CatalinSerafimescu/ZK-4KXPowerSupplyWithFan/KiCAD/board_3d.png

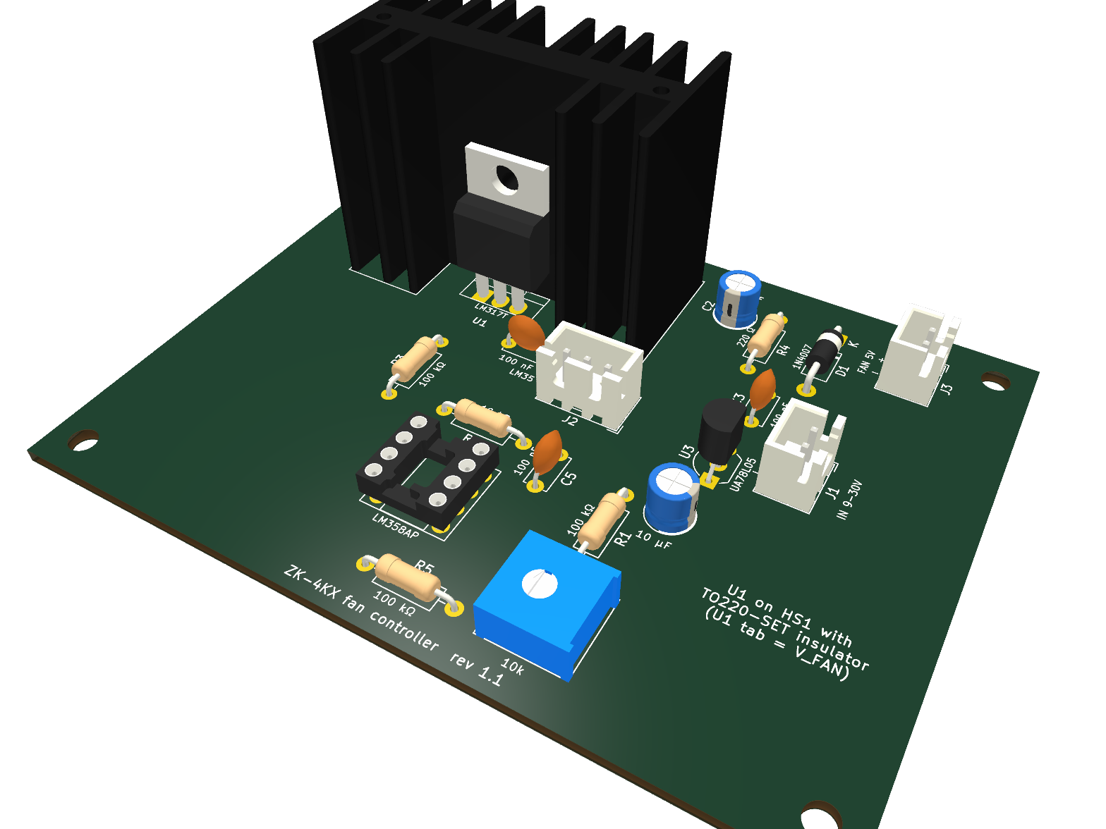
KiCAD/board_3d.png
