CatalinSerafimescu/ZK-4KXPowerSupplyWithFan/KiCAD/board_bottom.png

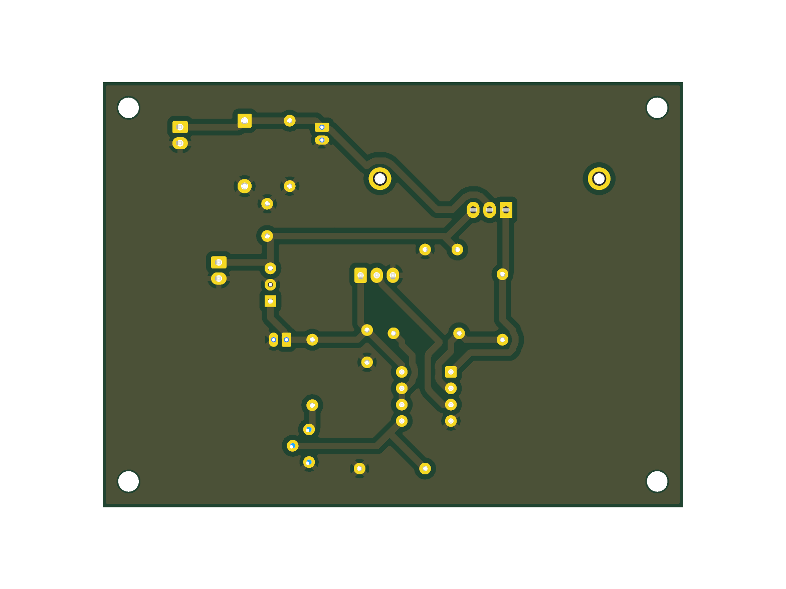
KiCAD/board_bottom.png
