CatalinSerafimescu/ZK-4KXPowerSupplyWithFan/KiCAD/board_top.png

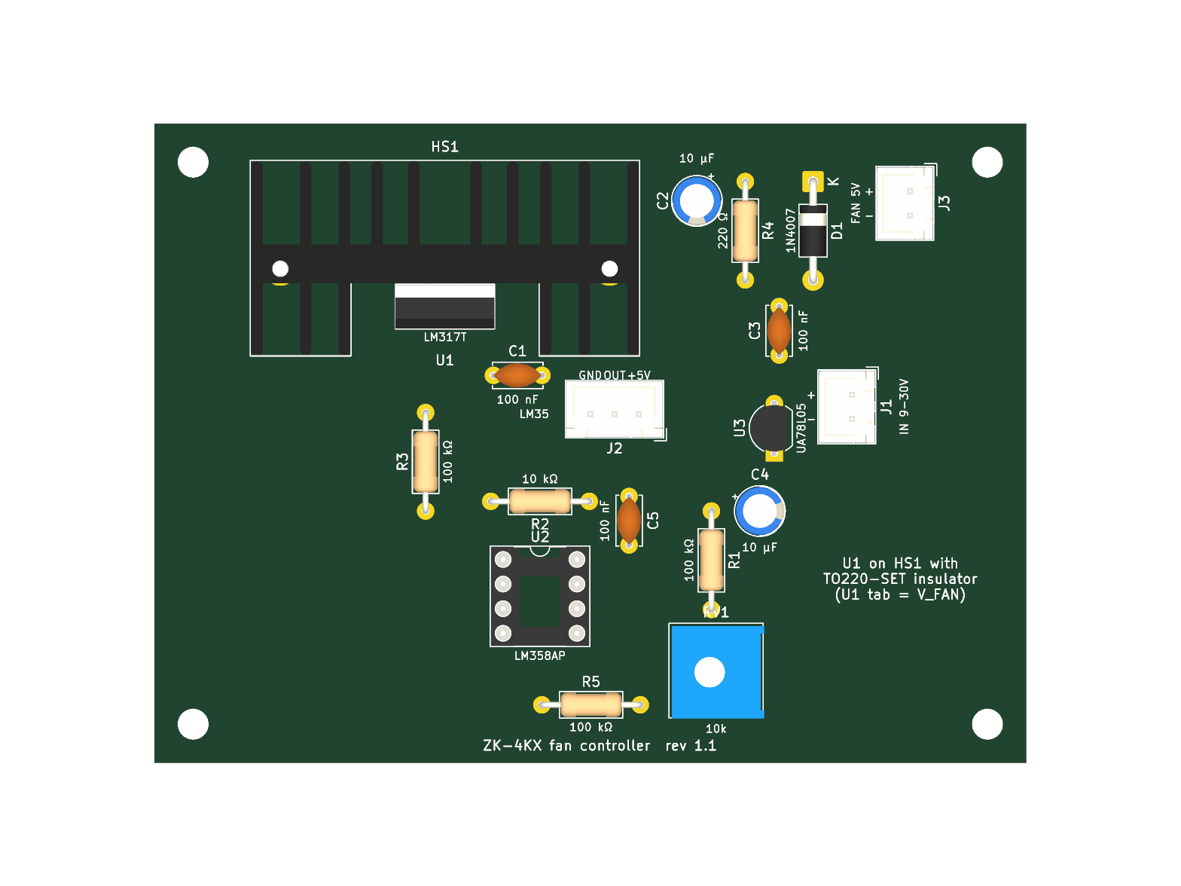
KiCAD/board_top.png
