CatalinSerafimescu/ZK-4KXPowerSupplyWithFan/mechanical/heatsink/RAD-DY-KY.jpg

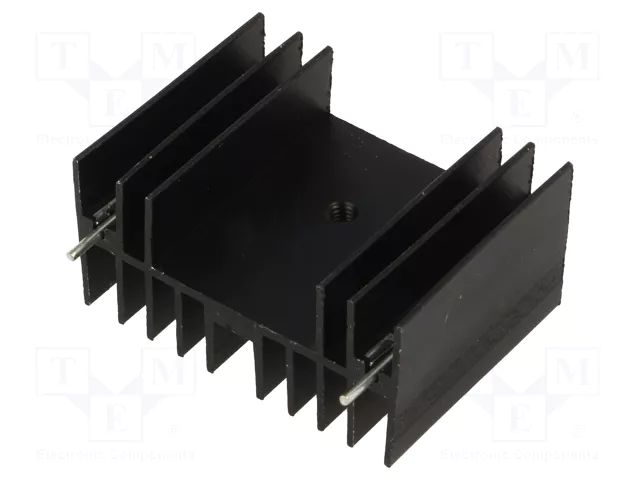
mechanical/heatsink/RAD-DY-KY.jpg
