CatalinSerafimescu/ZK-4KXPowerSupplyWithFan/mechanical/heatsink/RAD-DY-KY_top.jpg

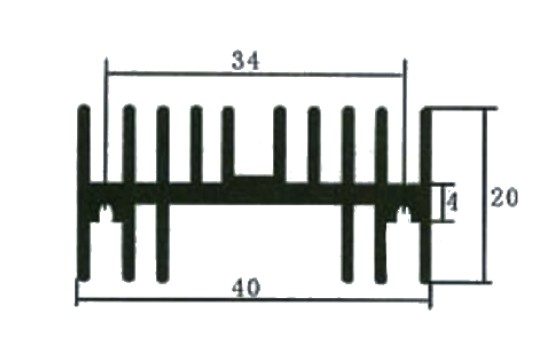
mechanical/heatsink/RAD-DY-KY_top.jpg
