CatalinSerafimescu/ZK-4KXPowerSupplyWithFan/simulation/ltspice/results/A_nominal_40C/out.csv

sweep | vin | t | v5 | vref | vadj | vfan | i317 | ifan
0.0 | 9.0 | 0.0 | 4.999919419615976 | 0.2852405573990915 | 0.006050843584329956 | 1.2532594928394667 | 0.05582701489726584 | 0.05013037971357867
0.25 | 9.0 | 0.25 | 4.999919419615976 | 0.2852405573990915 | 0.006050843584329956 | 1.2532594928394667 | 0.05582701489726584 | 0.05013037971357867
0.5 | 9.0 | 0.5 | 4.999919419615976 | 0.2852405573990915 | 0.006050843584329956 | 1.2532594928394667 | 0.05582701489726584 | 0.05013037971357867
0.75 | 9.0 | 0.75 | 4.999919419615976 | 0.2852405573990915 | 0.006050843584329956 | 1.2532594928394667 | 0.05582701489726584 | 0.05013037971357867
1.0 | 9.0 | 1.0 | 4.999919419615976 | 0.2852405573990915 | 0.006050843584329956 | 1.2532594928394667 | 0.05582701489726584 | 0.05013037971357867
1.25 | 9.0 | 1.25 | 4.999919419615976 | 0.2852405573990915 | 0.006050843584329956 | 1.2532594928394667 | 0.05582701489726584 | 0.05013037971357867
1.5 | 9.0 | 1.5 | 4.999919419615976 | 0.2852405573990915 | 0.006050843584329956 | 1.2532594928394667 | 0.05582701489726584 | 0.05013037971357867
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
