CatalinSerafimescu/ZK-4KXPowerSupplyWithFan/simulation/ltspice/results/B_pot_min/out.csv

sweep | vin | t | v5 | vref | vadj | vfan | i317 | ifan
0.0 | 9.0 | 0.0 | 4.999919436618777 | 0.005001899636495819 | 0.00599990036350418 | 1.253208662830933 | 0.05582475065142607 | 0.05012834651323732
0.25 | 9.0 | 0.25 | 4.999919436618777 | 0.005001899636495819 | 0.00599990036350418 | 1.253208662830933 | 0.05582475065142607 | 0.05012834651323732
0.5 | 9.0 | 0.5 | 4.999919436618777 | 0.005001899636495819 | 0.00599990036350418 | 1.253208662830933 | 0.05582475065142607 | 0.05012834651323732
0.75 | 9.0 | 0.75 | 4.999919436618777 | 0.005005888762806251 | 0.02794408419719705 | 1.2751040795998945 | 0.05680009194605117 | 0.05100416318399578
1.0 | 9.0 | 1.0 | 4.999919436618777 | 0.0050108782238625785 | 0.05539110946817133 | 1.3024901087149756 | 0.05802001506391612 | 0.052099604348599025
1.25 | 9.0 | 1.25 | 4.999919436618777 | 0.005015867684919205 | 0.08283813474070284 | 1.3298761378316104 | 0.05923993818185027 | 0.05319504551326442
1.5 | 9.0 | 1.5 | 4.999919436618777 | 0.005020857145975935 | 0.1102851600134869 | 1.3572621669484972 | 0.06045986129979565 | 0.05429048667793989
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
