CatalinSerafimescu/ZK-4KXPowerSupplyWithFan/simulation/ltspice/results/C_pot_max/out.csv

sweep | vin | t | v5 | vref | vadj | vfan | i317 | ifan
0.0 | 9.0 | 0.0 | 4.9999193991156305 | 0.4170312239474746 | 0.006074801167778126 | 1.253283397181426 | 0.05582807972704641 | 0.05013133588725704
0.25 | 9.0 | 0.25 | 4.9999193991156305 | 0.41703122394747455 | 0.006074801167778126 | 1.253283397181426 | 0.05582807972704641 | 0.05013133588725704
0.5 | 9.0 | 0.5 | 4.9999193991156305 | 0.41703122394747455 | 0.006074801167778126 | 1.253283397181426 | 0.05582807972704641 | 0.05013133588725704
0.75 | 9.0 | 0.75 | 4.9999193991156305 | 0.41703122394747455 | 0.006074801167778126 | 1.253283397181426 | 0.05582807972704641 | 0.05013133588725704
1.0 | 9.0 | 1.0 | 4.9999193991156305 | 0.41703122394747455 | 0.006074801167778126 | 1.253283397181426 | 0.05582807972704641 | 0.05013133588725704
1.25 | 9.0 | 1.25 | 4.9999193991156305 | 0.41703122394747455 | 0.006074801167778126 | 1.253283397181426 | 0.05582807972704641 | 0.05013133588725704
1.5 | 9.0 | 1.5 | 4.9999193991156305 | 0.41703122394747455 | 0.006074801167778126 | 1.253283397181426 | 0.05582807972704641 | 0.05013133588725704
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
