CatalinSerafimescu/ZK-4KXPowerSupplyWithFan/simulation/ltspice/results/D_vin_sweep_hot/out.csv

sweep | vin | t | v5 | vref | vadj | vfan | i317 | ifan
6.0 | 6.0 | 70.0 | 4.299920058395359 | 0.24534338399765432 | 2.800455574360747 | 4.041454153675535 | 0.18002841370423747 | 0.16165816614702141
6.05 | 6.05 | 70.0 | 4.349920012768259 | 0.2481931825606314 | 2.8504469575364455 | 4.091334439849959 | 0.18225035372972256 | 0.16365337759399837
6.1 | 6.1 | 70.0 | 4.399919967141161 | 0.25104298112360846 | 2.900438340712144 | 4.1412147260243835 | 0.18447229375520768 | 0.16564858904097535
6.15 | 6.15 | 70.0 | 4.449919921514062 | 0.25389277968658563 | 2.9504297238878427 | 4.191095012198808 | 0.1866942337806928 | 0.16764380048795233
6.2 | 6.2 | 70.0 | 4.499919875886963 | 0.2567425782495627 | 3.0004211070635423 | 4.240975298373233 | 0.18891617380617798 | 0.16963901193492933
6.25 | 6.25 | 70.0 | 4.5499198302598645 | 0.2595923768125398 | 3.050412490239241 | 4.290855584547658 | 0.1911381138316631 | 0.17163422338190631
6.3 | 6.3 | 70.0 | 4.599919784632766 | 0.26244217537551695 | 3.1004038734149395 | 4.3407358707220824 | 0.19336005385714822 | 0.1736294348288833
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
