CatalinSerafimescu/ZK-4KXPowerSupplyWithFan/simulation/ltspice/results/E_powerup_9V_hot/out.csv

sweep | vin | t | v5 | vref | vadj | vfan | i317 | ifan
0.0 | 0.0 | 70.0 | -7.600893063859696e-05 | -1.5000741092941428 | -1.4990761085671345 | 0.0 | 0.0 | 0.0
2.9296876036255526e-10 | 0.0 | 70.0 | -7.600893063859693e-05 | -1.5000741092941428 | -1.4990761085671345 | 0.0 | 0.0 | 0.0
5.859375207251105e-10 | 0.0 | 70.0 | -7.600893063859691e-05 | -1.5000741092941428 | -1.4990761085671345 | 0.0 | 0.0 | 0.0
1.171875041450221e-09 | 0.0 | 70.0 | -7.600893063859687e-05 | -1.5000741092941428 | -1.4990761085671345 | 0.0 | 0.0 | 0.0
2.343750082900442e-09 | 0.0 | 70.0 | -7.600893063859682e-05 | -1.5000741092941428 | -1.4990761085671345 | 0.0 | 0.0 | 0.0
4.687500165800884e-09 | 0.0 | 70.0 | -7.600893063859675e-05 | -1.5000741092941428 | -1.4990761085671345 | 0.0 | 0.0 | 0.0
9.375000331601768e-09 | 0.0 | 70.0 | -7.600893063859671e-05 | -1.5000741092941428 | -1.4990761085671345 | 0.0 | 0.0 | 0.0
1.8750000663203537e-08 | 0.0 | 70.0 | -7.600893063859671e-05 | -1.5000741092941428 | -1.4990761085671345 | 0.0 | 0.0 | 0.0
3.750000132640707e-08 | 0.0 | 70.0 | -7.600893063859671e-05 | -1.5000741092941428 | -1.4990761085671345 | 0.0 | 0.0 | 0.0
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
