CatalinSerafimescu/ZK-4KXPowerSupplyWithFan/simulation/ltspice/results/A_nominal_40C/plot.png

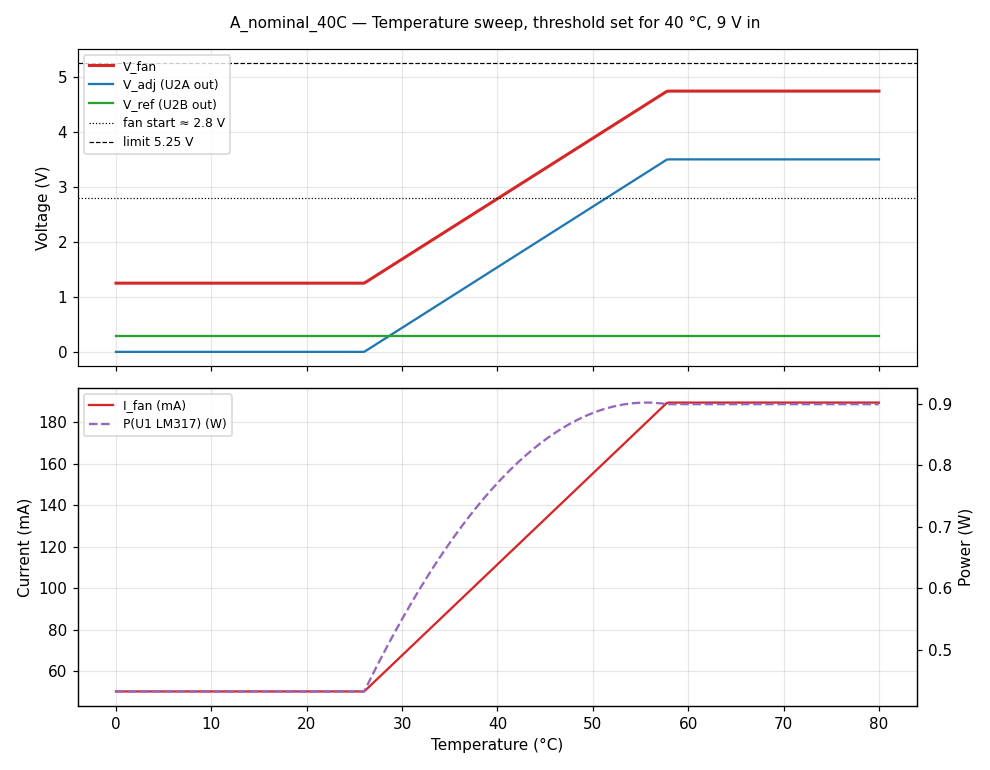
simulation/ltspice/results/A_nominal_40C/plot.png
