CatalinSerafimescu/ZK-4KXPowerSupplyWithFan/simulation/ltspice/results/B_pot_min/plot.png

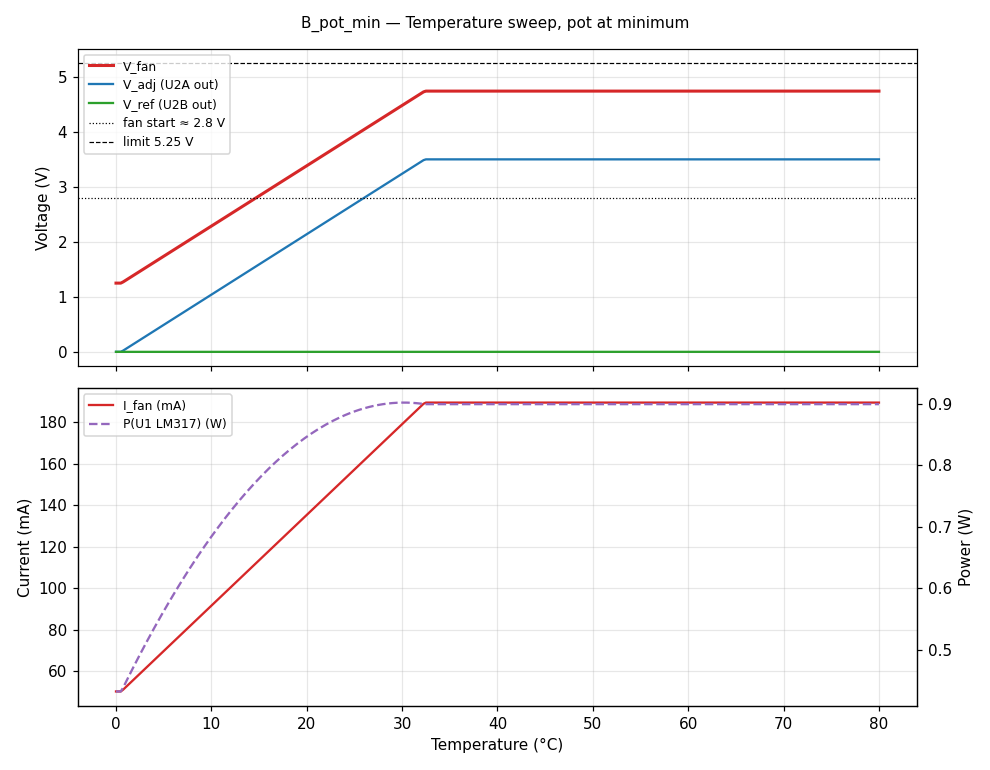
simulation/ltspice/results/B_pot_min/plot.png
