CatalinSerafimescu/ZK-4KXPowerSupplyWithFan/simulation/ltspice/results/C_pot_max/plot.png

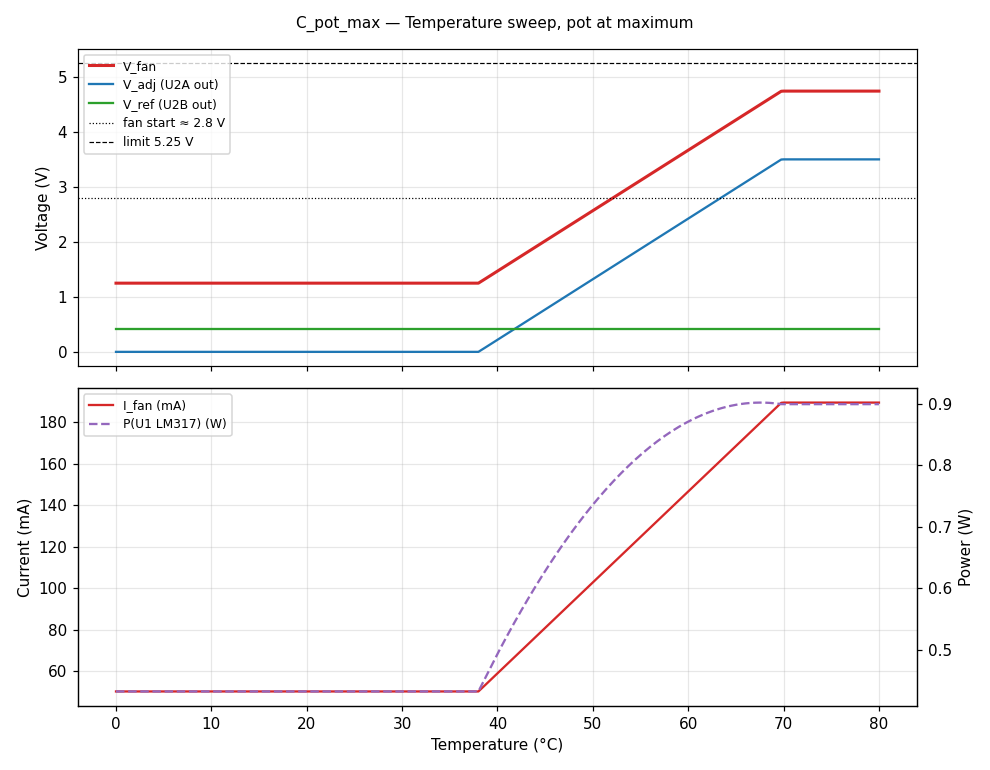
simulation/ltspice/results/C_pot_max/plot.png
