CatalinSerafimescu/ZK-4KXPowerSupplyWithFan/simulation/ltspice/results/D_vin_sweep_hot/plot.png

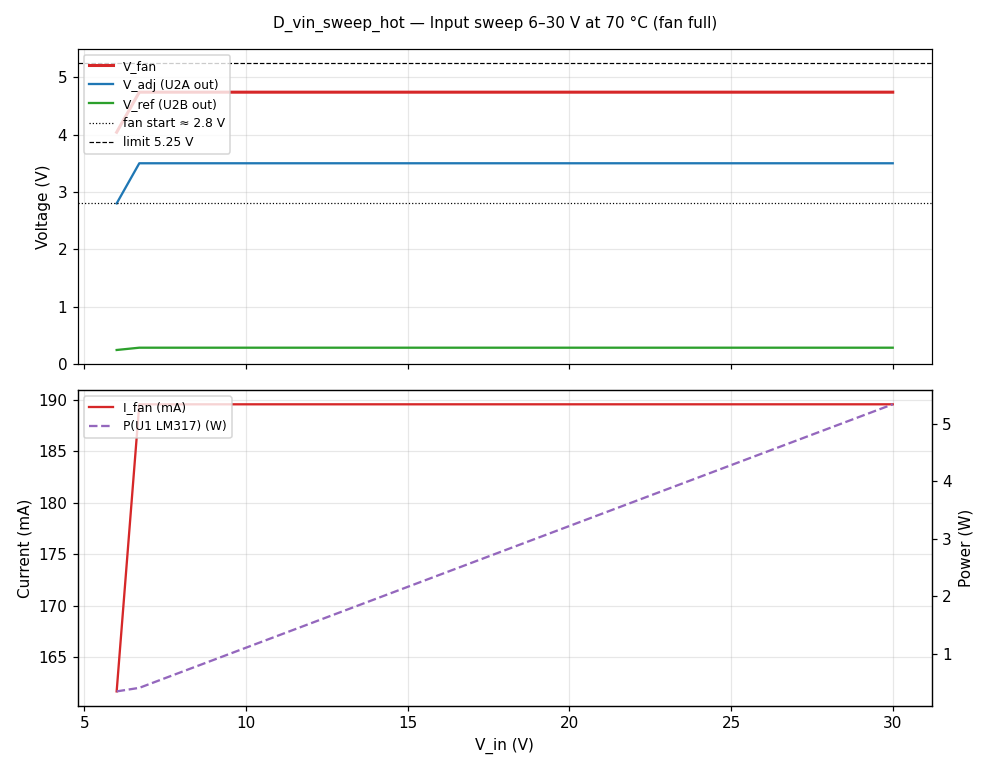
simulation/ltspice/results/D_vin_sweep_hot/plot.png
