CatalinSerafimescu/ZK-4KXPowerSupplyWithFan/simulation/ltspice/results/E_powerup_9V_hot/plot.png

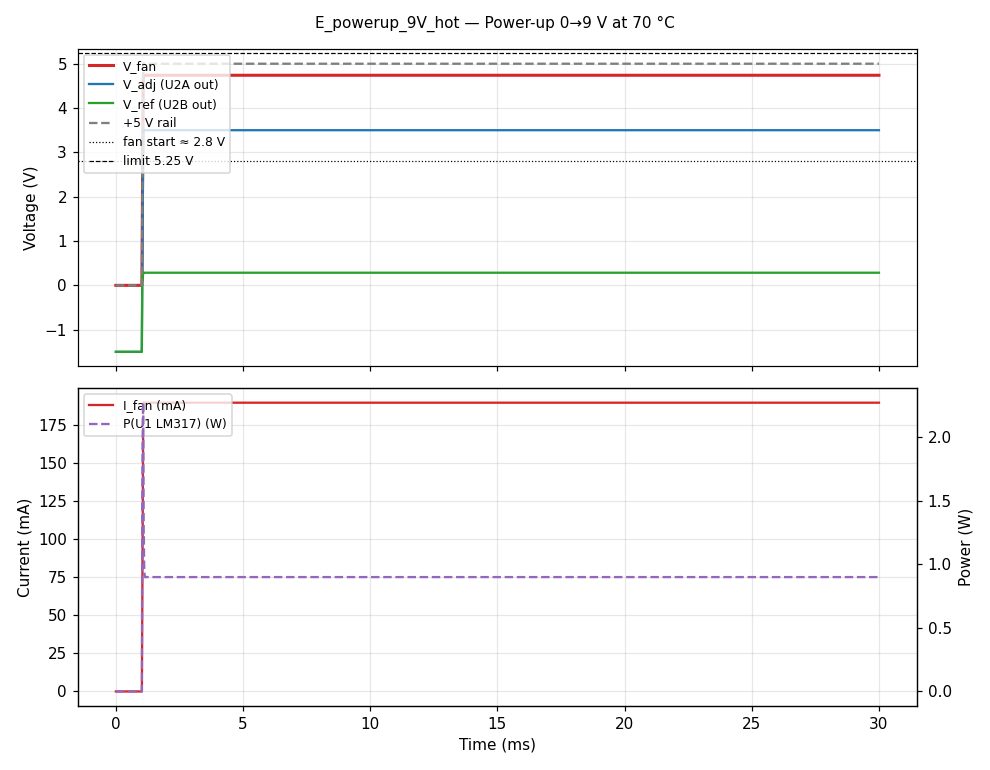
simulation/ltspice/results/E_powerup_9V_hot/plot.png
