CatalinSerafimescu/ZK-4KXPowerSupplyWithFan/simulation/ltspice/results/G_powerup_9V_cold/plot.png

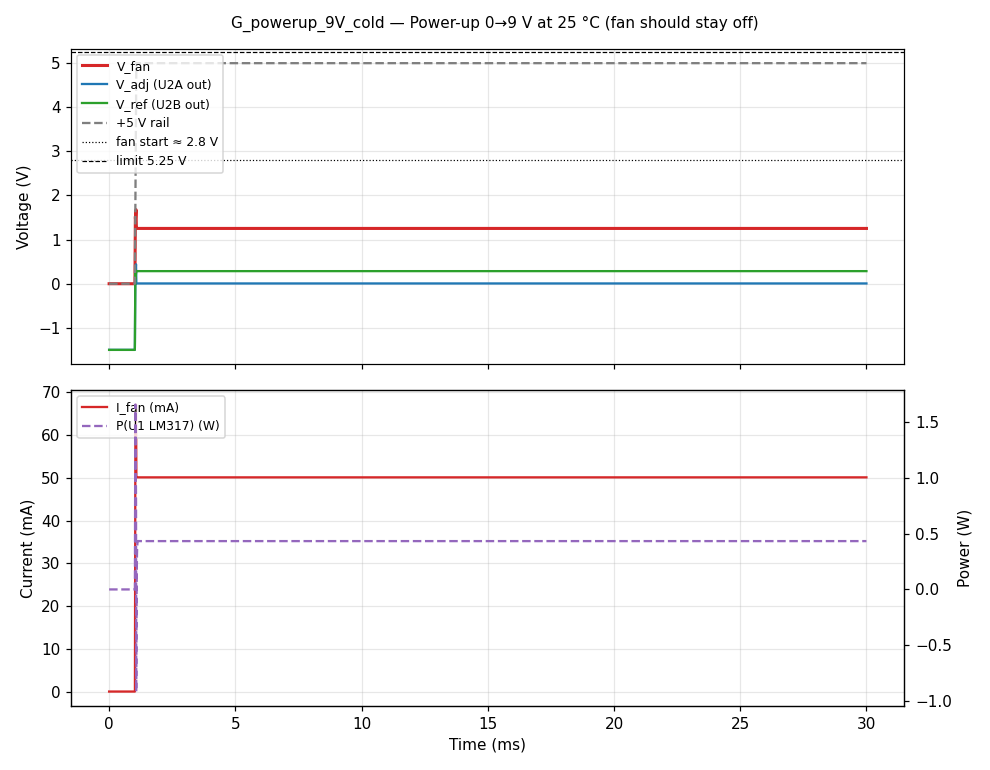
simulation/ltspice/results/G_powerup_9V_cold/plot.png
