CatalinSerafimescu/ZK-4KXPowerSupplyWithFan/simulation/ltspice/results/H_wiper_open/plot.png

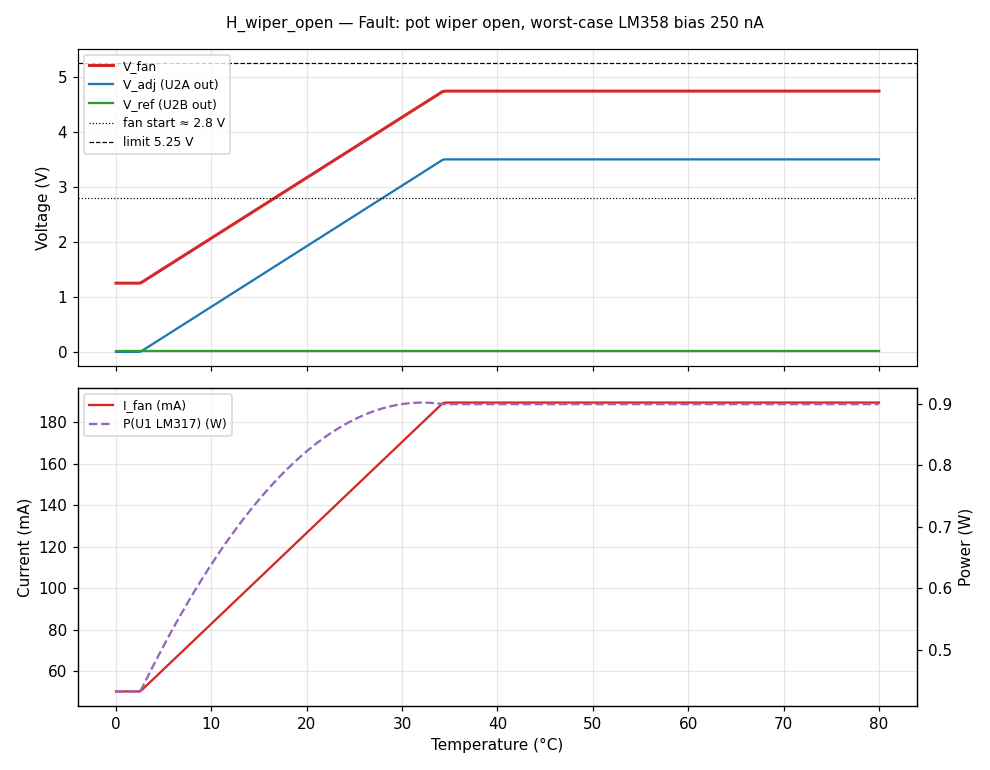
simulation/ltspice/results/H_wiper_open/plot.png
