CatalinSerafimescu/ZK-4KXPowerSupplyWithFan/simulation/ltspice/results/I_sensor_open/plot.png

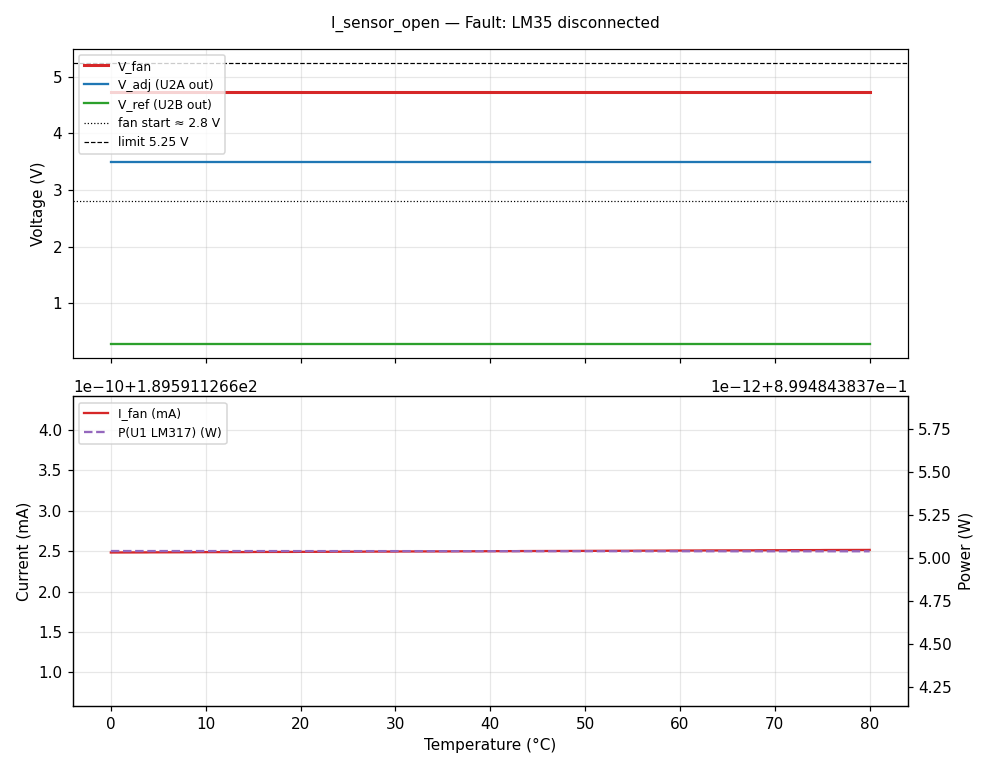
simulation/ltspice/results/I_sensor_open/plot.png
