CatalinSerafimescu/ZK-4KXPowerSupplyWithFan/simulation/ltspice/results/J_offset_worst_pos/plot.png

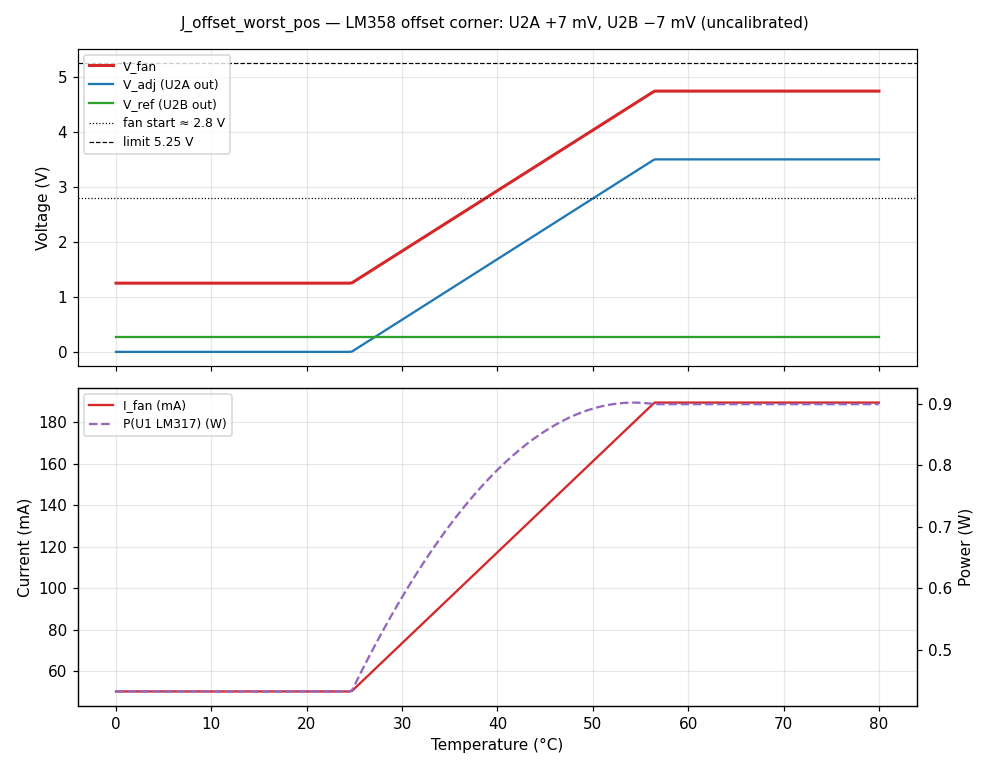
simulation/ltspice/results/J_offset_worst_pos/plot.png
