CatalinSerafimescu/ZK-4KXPowerSupplyWithFan/simulation/ltspice/results_vendor/B_pot_min/plot.png

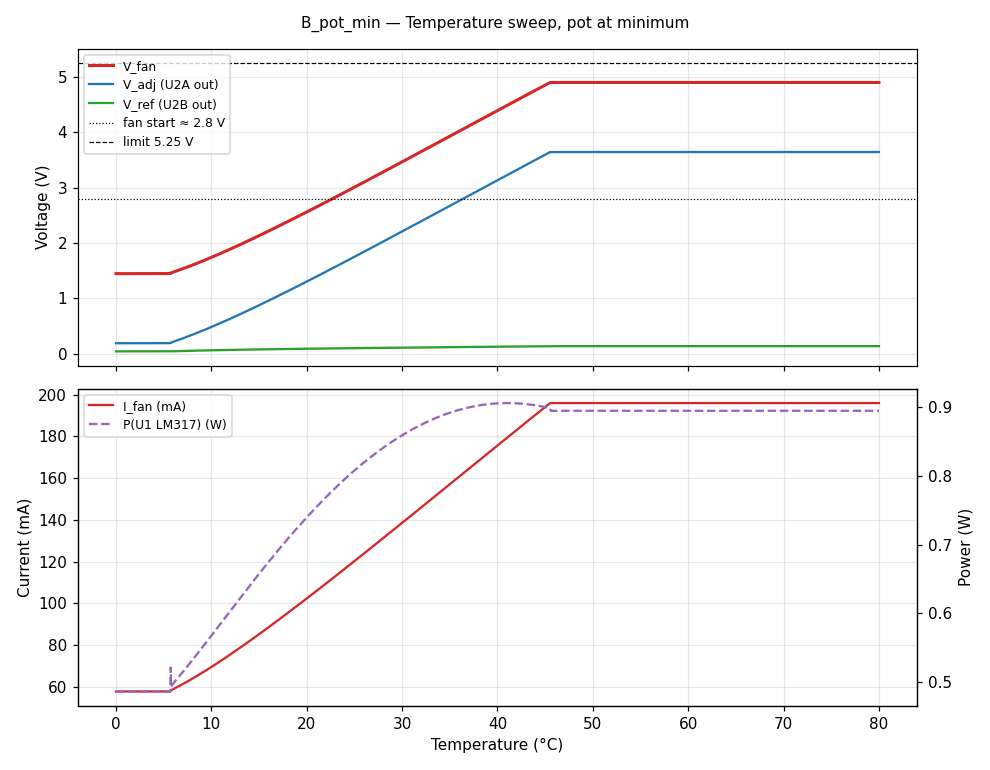
simulation/ltspice/results_vendor/B_pot_min/plot.png
