CatalinSerafimescu/ZK-4KXPowerSupplyWithFan/simulation/ltspice/results_vendor/G_powerup_9V_cold/plot.png

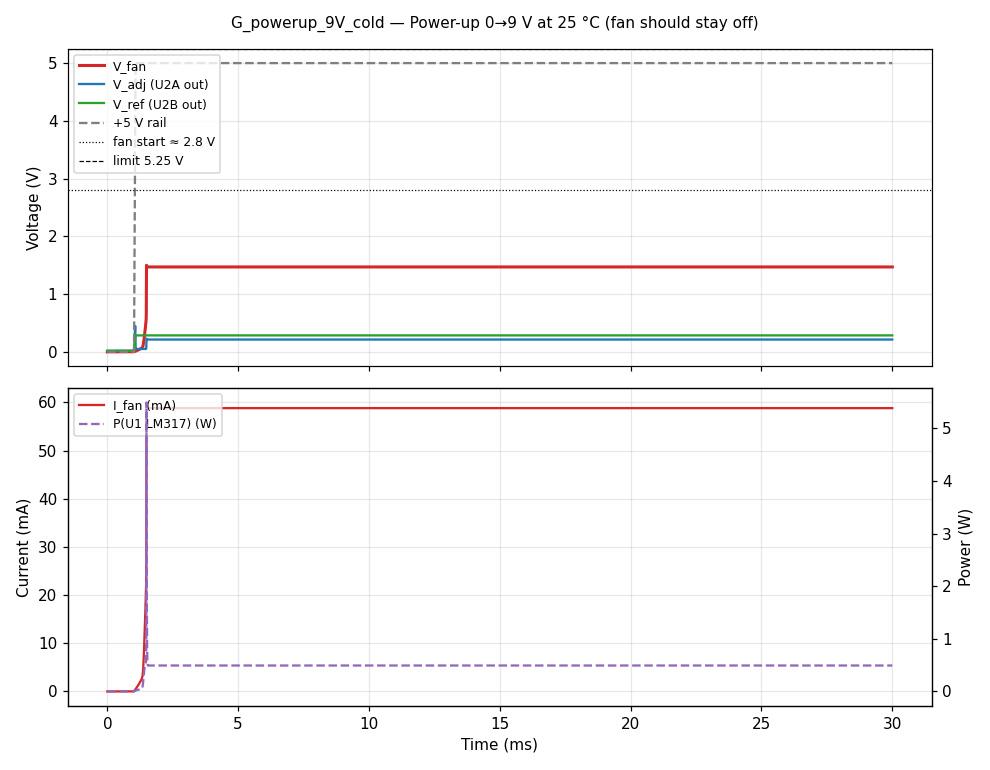
simulation/ltspice/results_vendor/G_powerup_9V_cold/plot.png
