CatalinSerafimescu/ZK-4KXPowerSupplyWithFan/simulation/ltspice/results_vendor/J_offset_worst_pos/plot.png

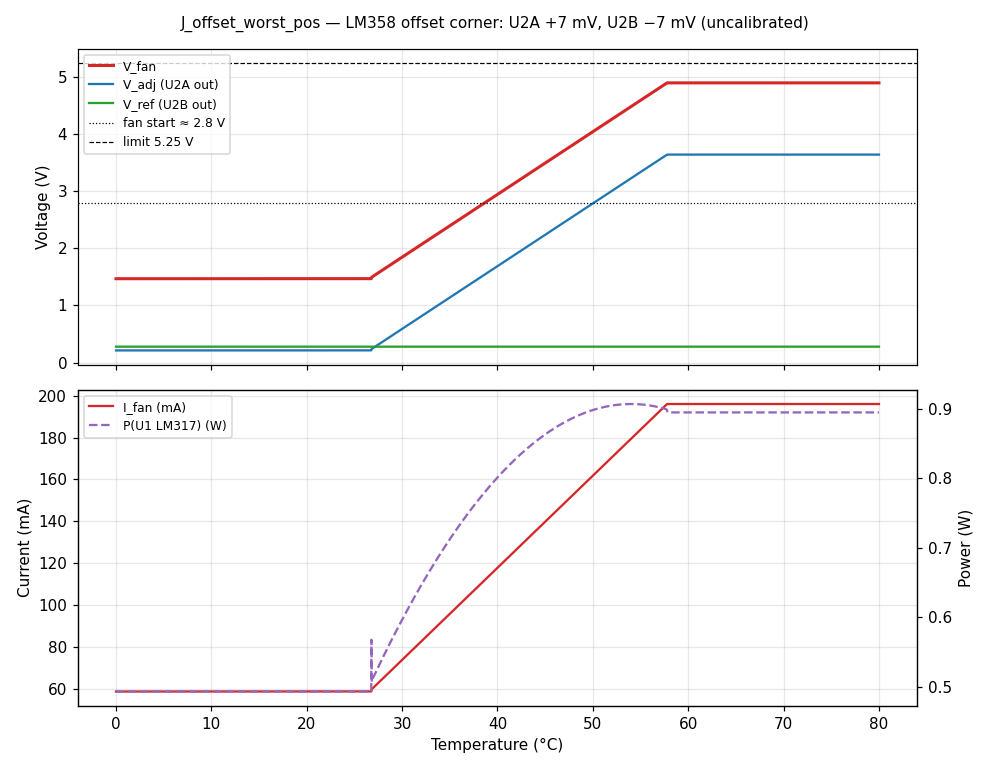
simulation/ltspice/results_vendor/J_offset_worst_pos/plot.png
