CatalinSerafimescu/ZK-4KXPowerSupplyWithFan/simulation/ngspice/results/E_powerup_9V_hot/plot.png

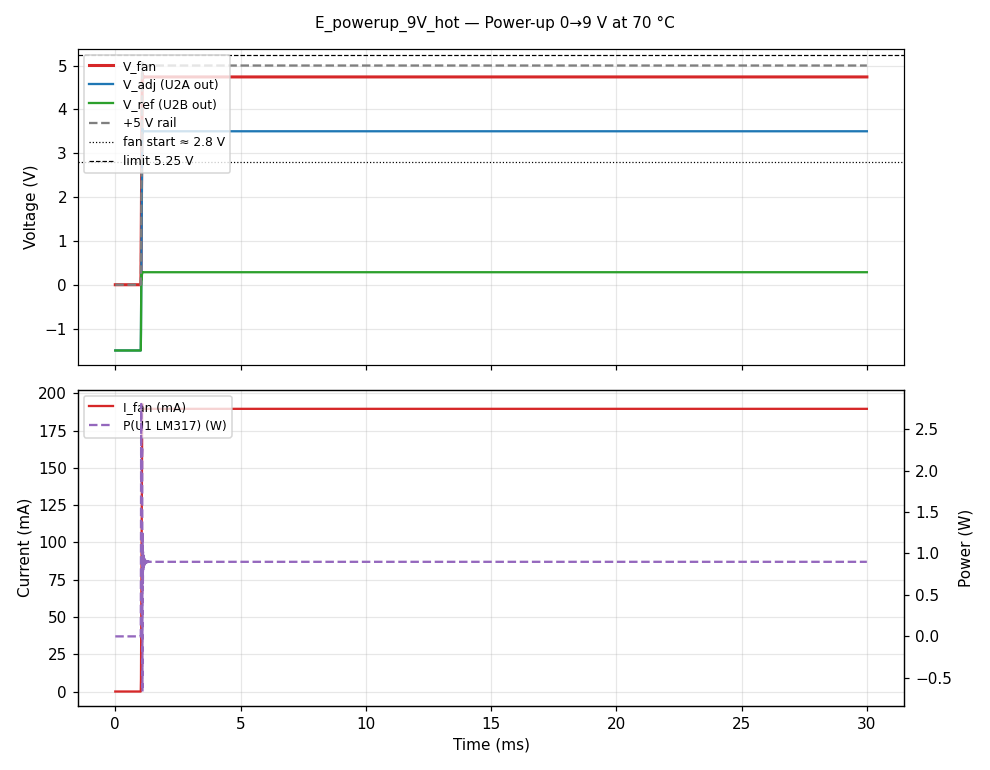
simulation/ngspice/results/E_powerup_9V_hot/plot.png
