CatalinSerafimescu/ZK-4KXPowerSupplyWithFan/simulation/ngspice/results/G_powerup_9V_cold/plot.png

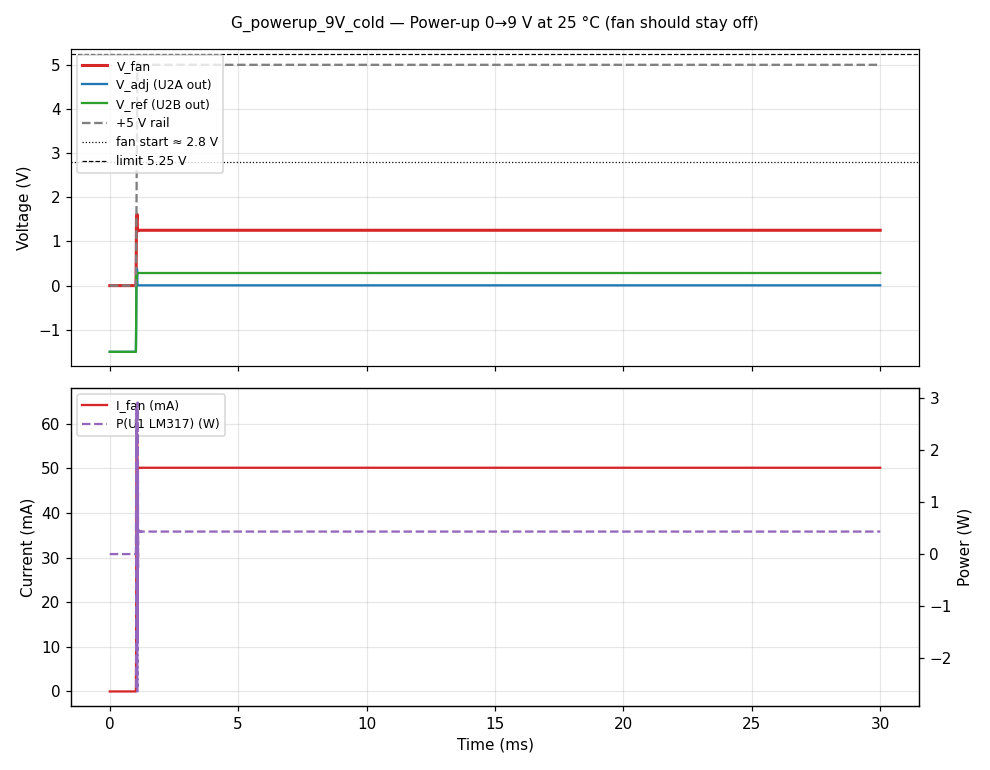
simulation/ngspice/results/G_powerup_9V_cold/plot.png
