CatalinSerafimescu/ZK-4KXPowerSupplyWithFan/simulation/ngspice/results/I_sensor_open/plot.png

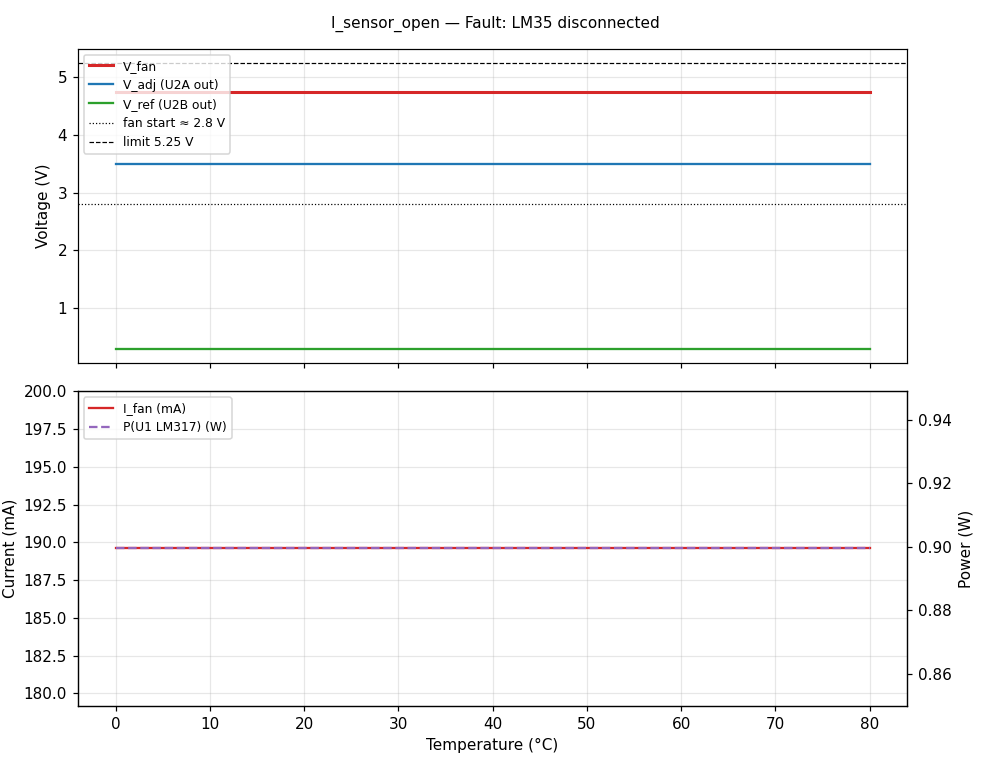
simulation/ngspice/results/I_sensor_open/plot.png
